Luddi96/WaterSens/Images/IMG_20200821_111452.jpg

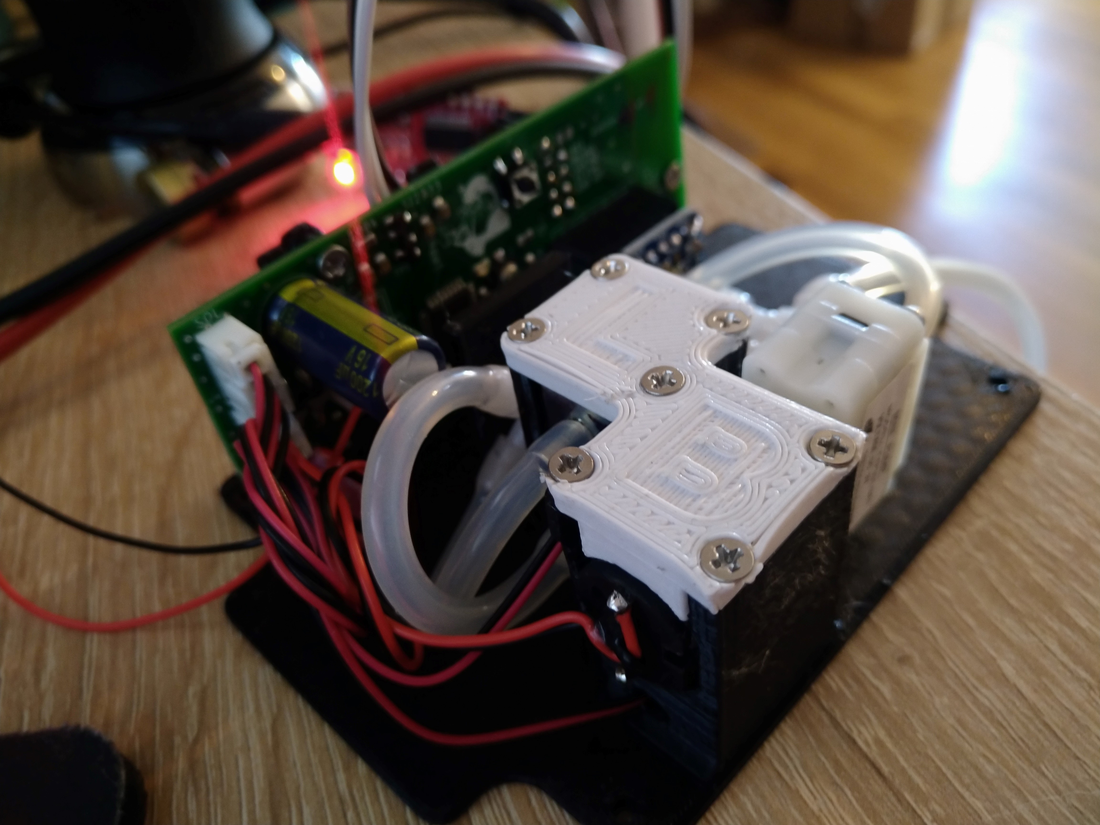
Images/IMG_20200821_111452.jpg
