Luddi96/WaterSens/Images/IMG_20200907_204918_046.jpg

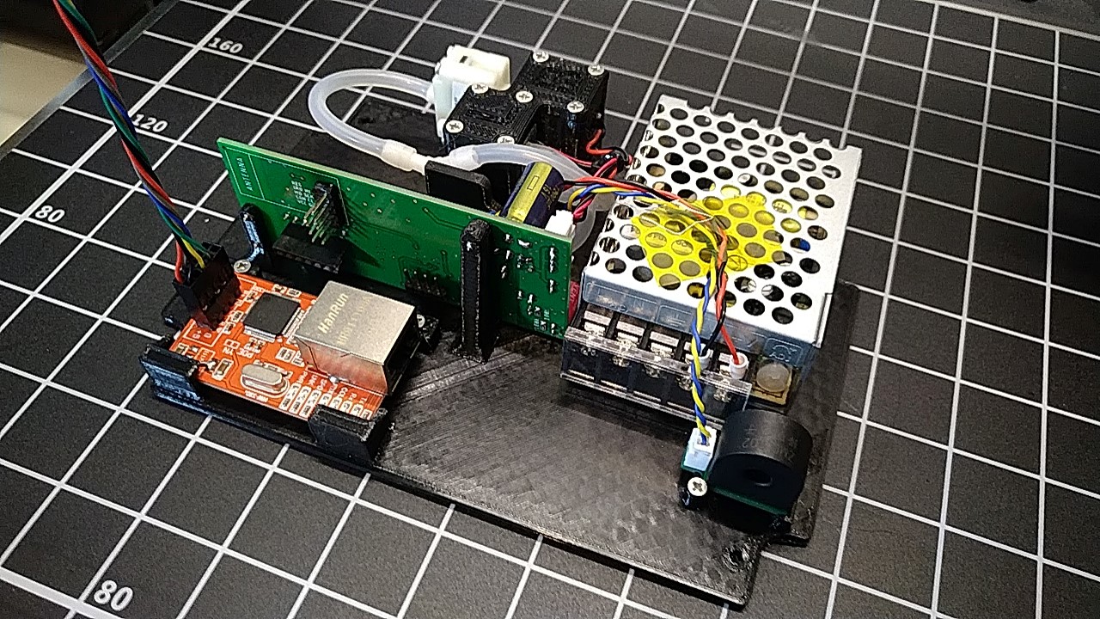
Images/IMG_20200907_204918_046.jpg
