Luddi96/WaterSens/Images/IMG_20200907_204925_896.jpg

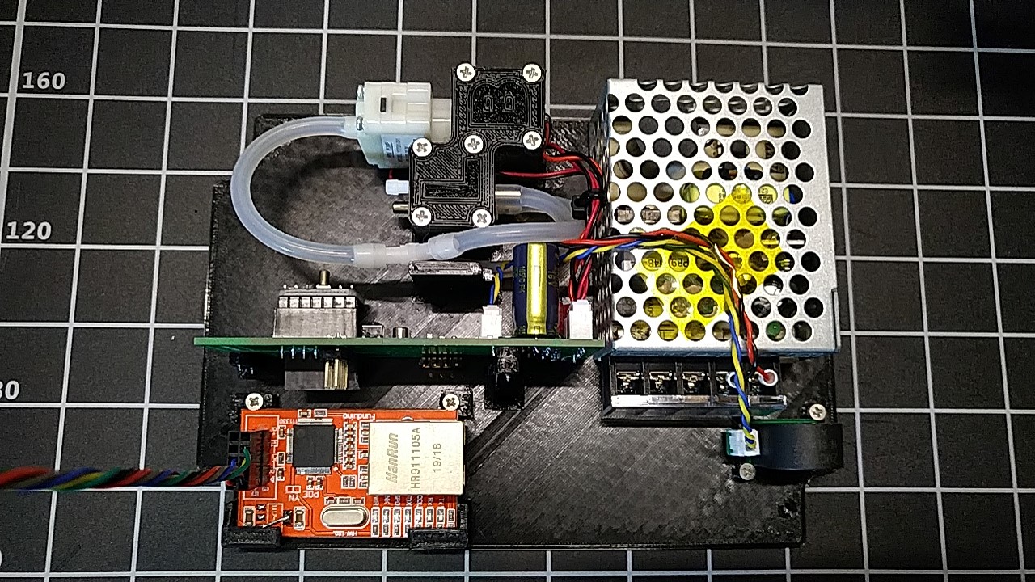
Images/IMG_20200907_204925_896.jpg
