Luddi96/WaterSens/Images/IMG_20200907_205103_475.jpg

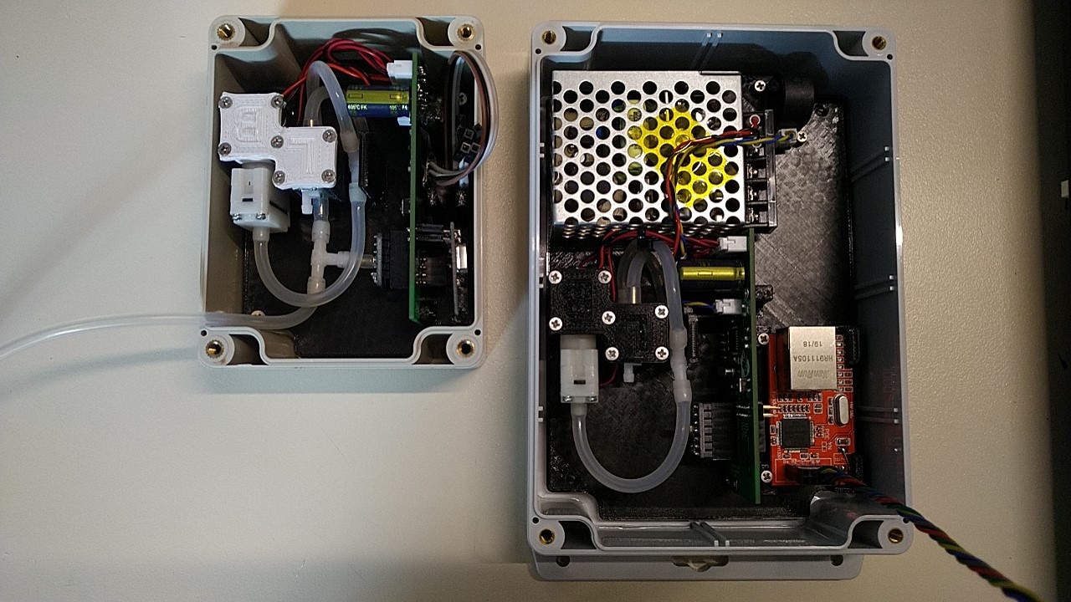
Images/IMG_20200907_205103_475.jpg
