Luddi96/WaterSens/Images/IMG_20200909_182001.jpg

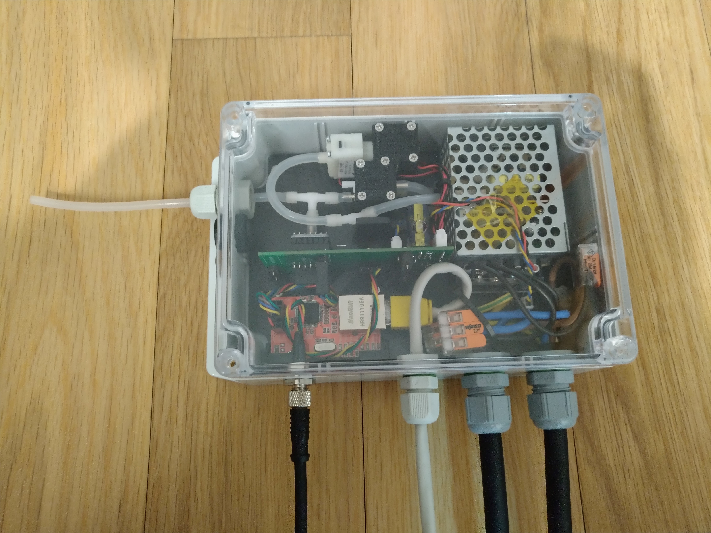
Images/IMG_20200909_182001.jpg
