Luddi96/WaterSens/Images/IMG_20200909_182011.jpg

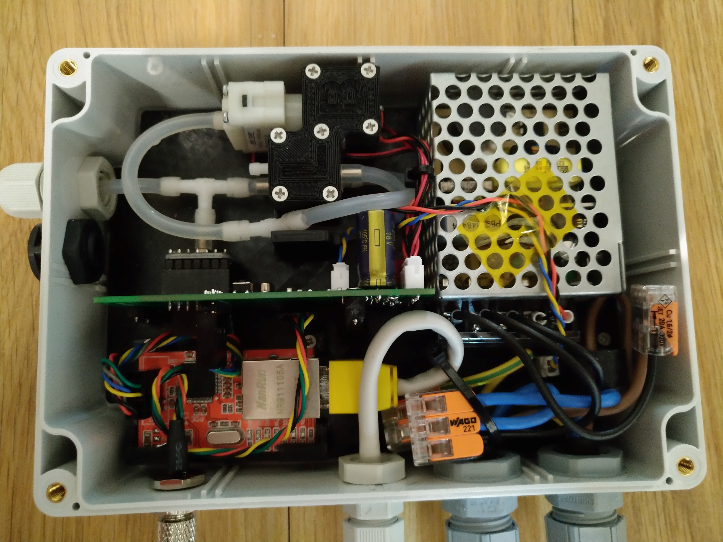
Images/IMG_20200909_182011.jpg
