Luddi96/WaterSens/Images/IMG_20210317_152709.jpg

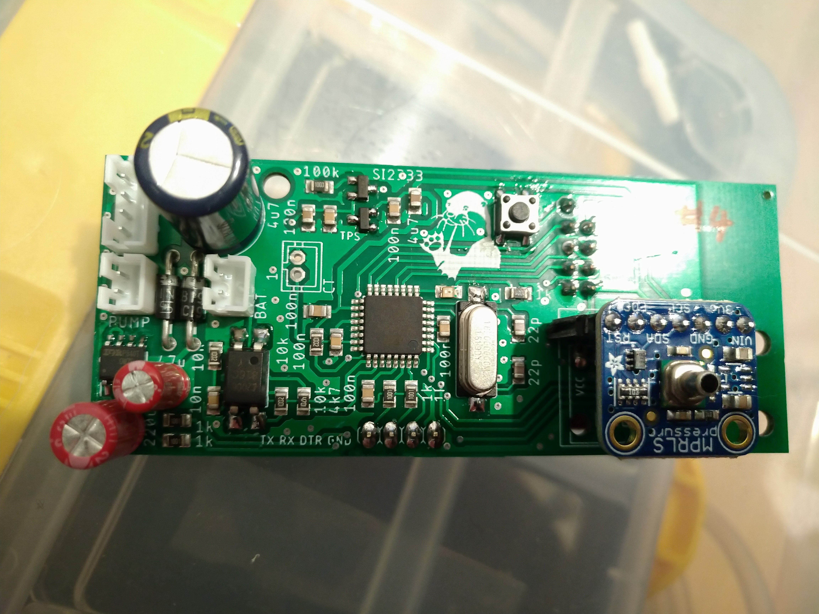
Images/IMG_20210317_152709.jpg
