Luddi96/WaterSens/Images/IMG_20210317_152739.jpg

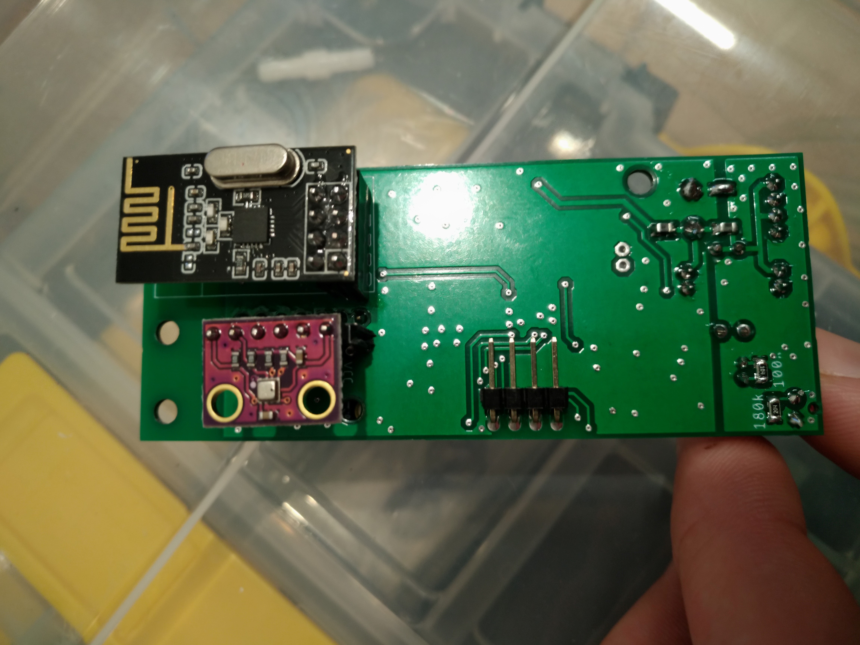
Images/IMG_20210317_152739.jpg
